Kislac/water-tank-monitor/Docs/1_SelectTankType.png

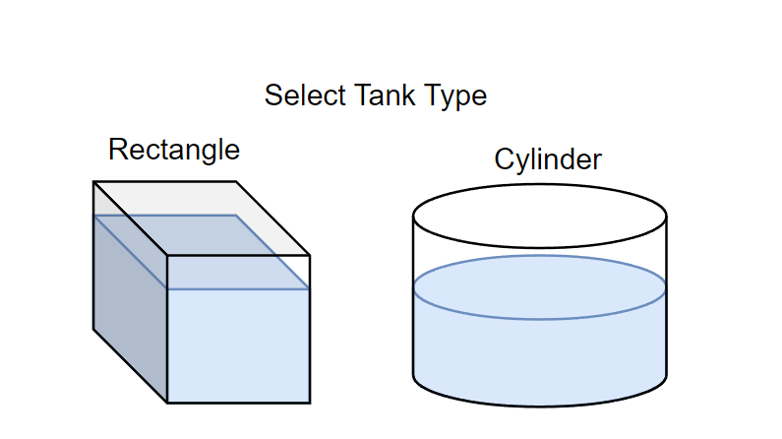
Docs/1_SelectTankType.png
