Kislac/water-tank-monitor/Docs/3_Cilinderdimensions.png

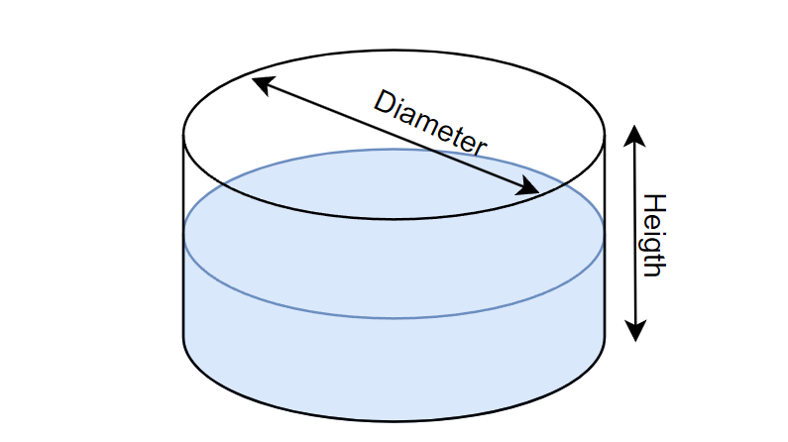
Docs/3_Cilinderdimensions.png
