Kislac/water-tank-monitor/Docs/4_TankFullEmpty.png

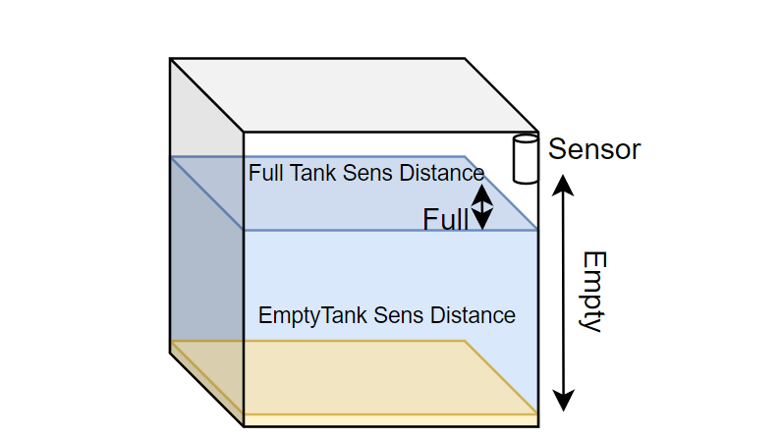
Docs/4_TankFullEmpty.png
