Kislac/water-tank-monitor/Docs/2025-04-12_16h48_50.png

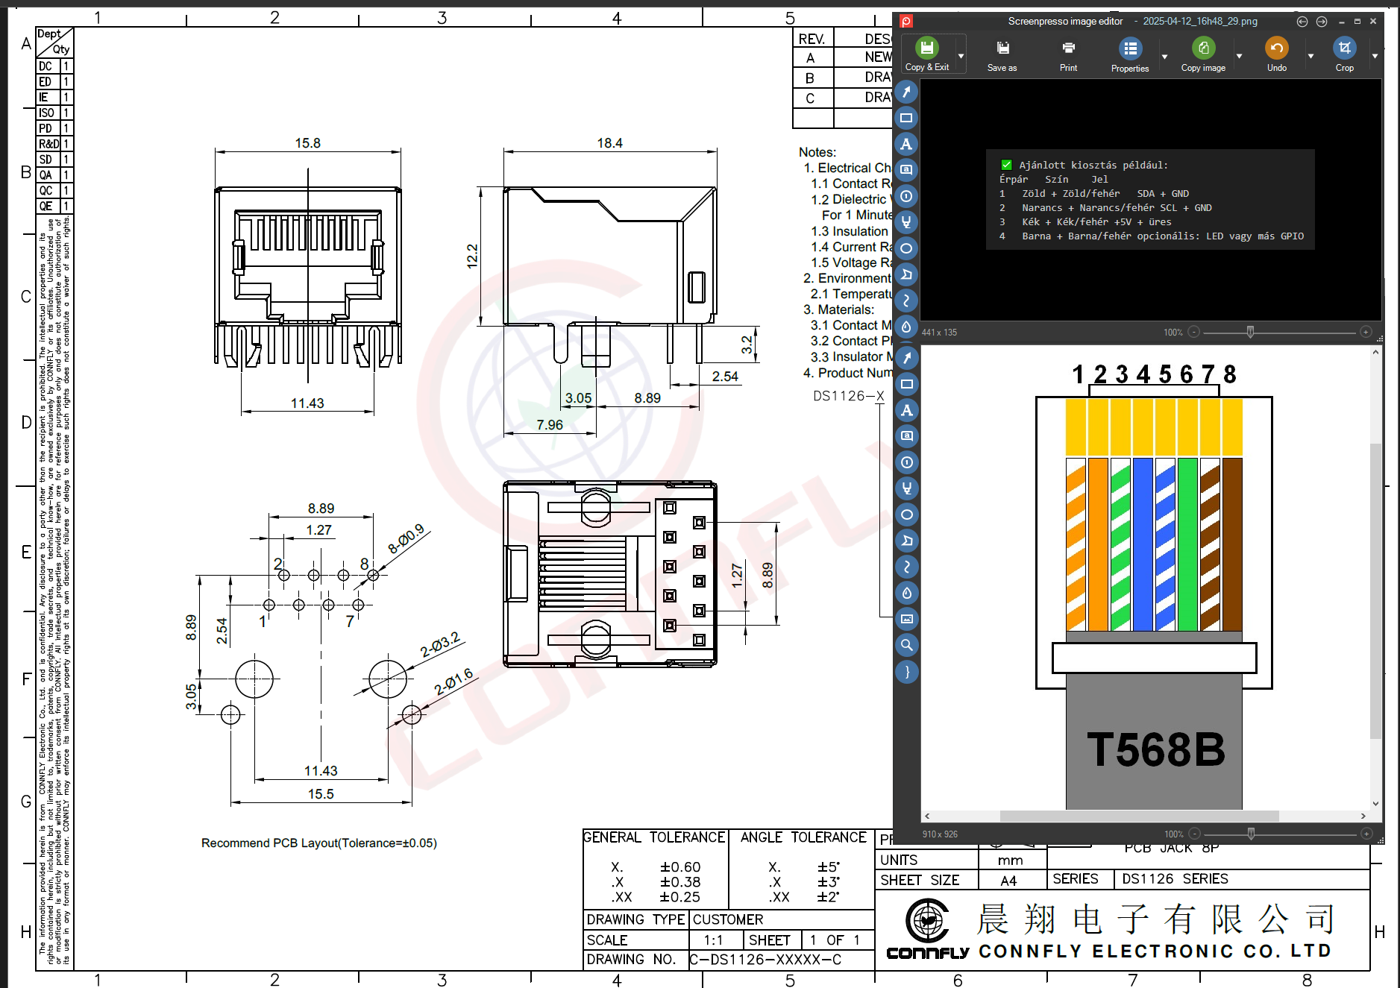
Docs/2025-04-12_16h48_50.png
