Kislac/water-tank-monitor/SquareLine/cache/thumb_3447910131_SelectTankType.png

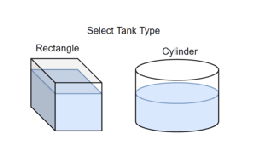
SquareLine/cache/thumb_3447910131_SelectTankType.png
