Kislac/water-tank-monitor/SquareLine/cache/thumb_10633528524_TankFullEmpty.png

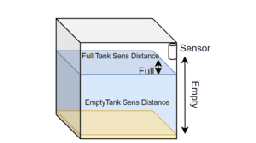
SquareLine/cache/thumb_10633528524_TankFullEmpty.png
