Kislac/water-tank-monitor/SquareLine/cache/thumb_20626862443_Cilinderdimensions.png

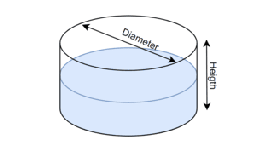
SquareLine/cache/thumb_20626862443_Cilinderdimensions.png
